neuroidss/FreeEEG32-alpha1.5/OpenVIBE/gdf/Screenshot from 2019-09-13 23-40-55.png

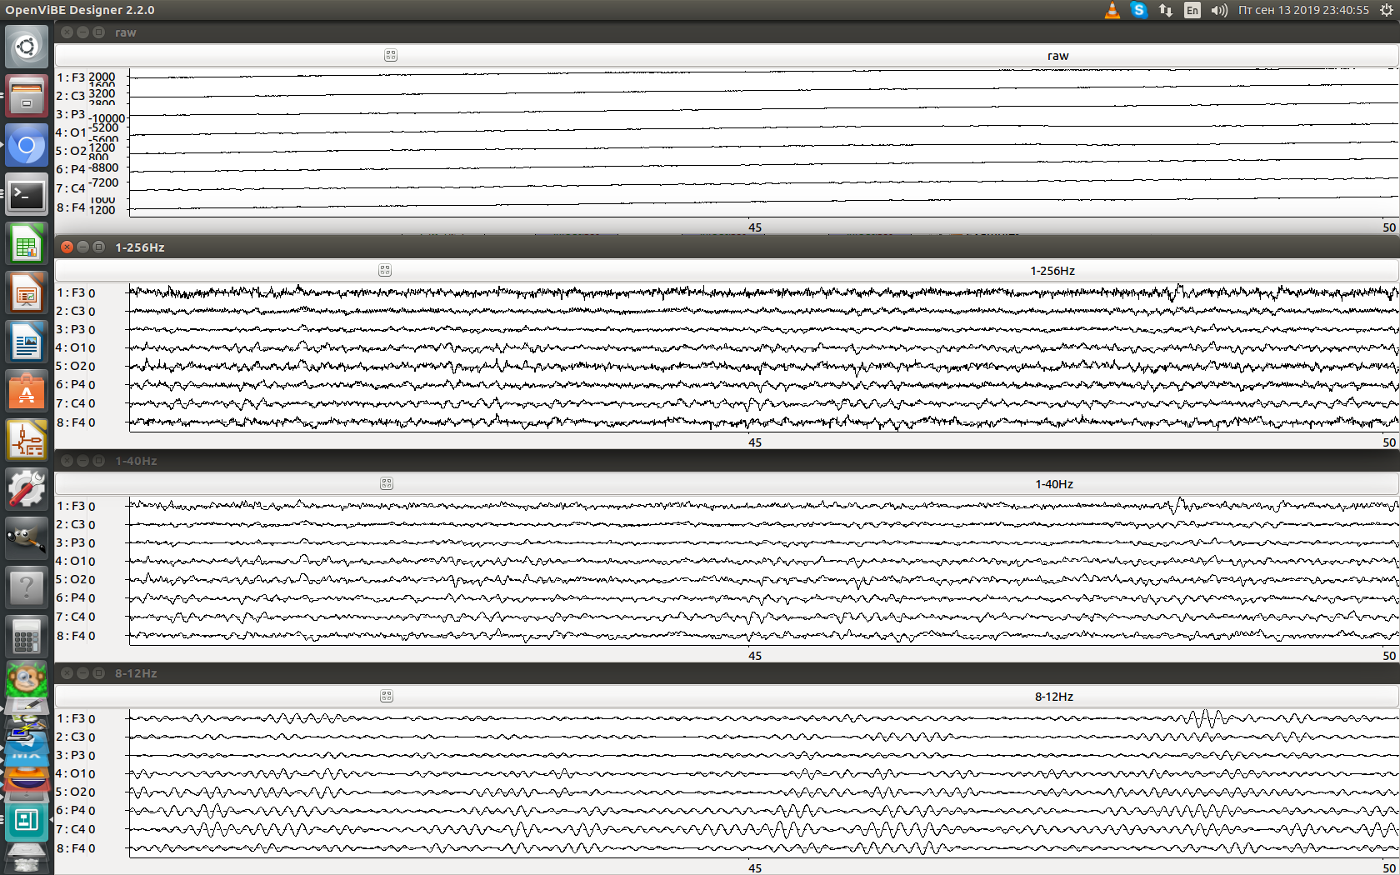
OpenVIBE/gdf/Screenshot from 2019-09-13 23-40-55.png
