neuroidss/FreeEEG32-alpha1.5/OpenVIBE/photo_2019-10-30_23-13-45.jpg

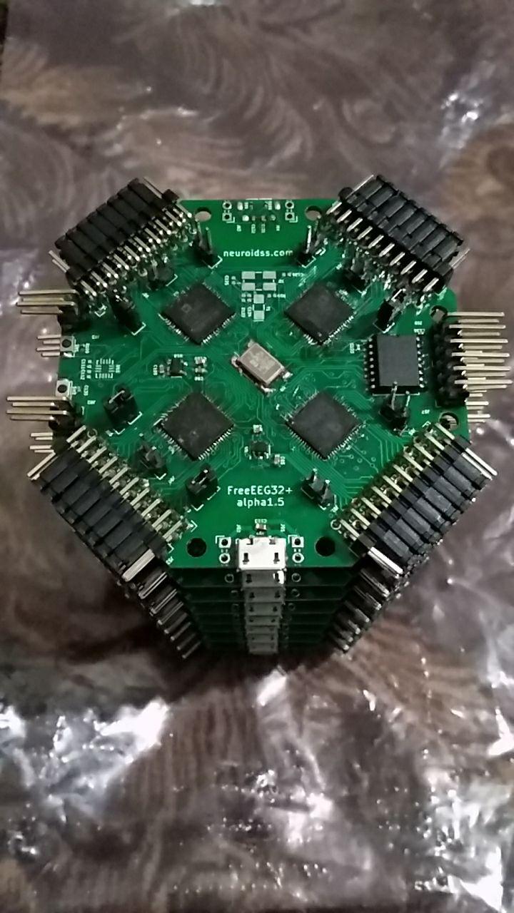
OpenVIBE/photo_2019-10-30_23-13-45.jpg
