neuroidss/FreeEEG32-alpha1.5/OpenVIBE/photo_2019-10-31_11-32-17.jpg

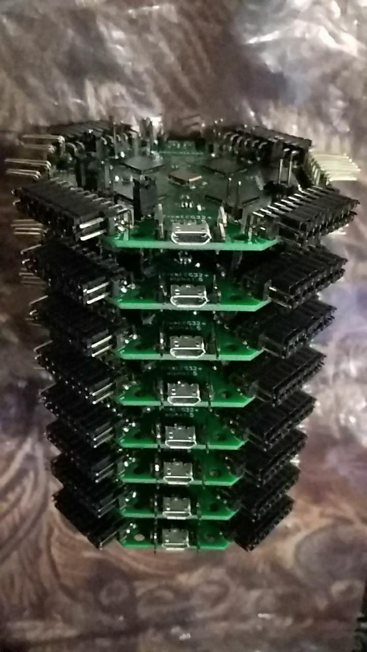
OpenVIBE/photo_2019-10-31_11-32-17.jpg
