neuroidss/FreeEEG32-alpha1.5/OpenVIBE/Screenshot from 2019-09-04 21-14-45.png

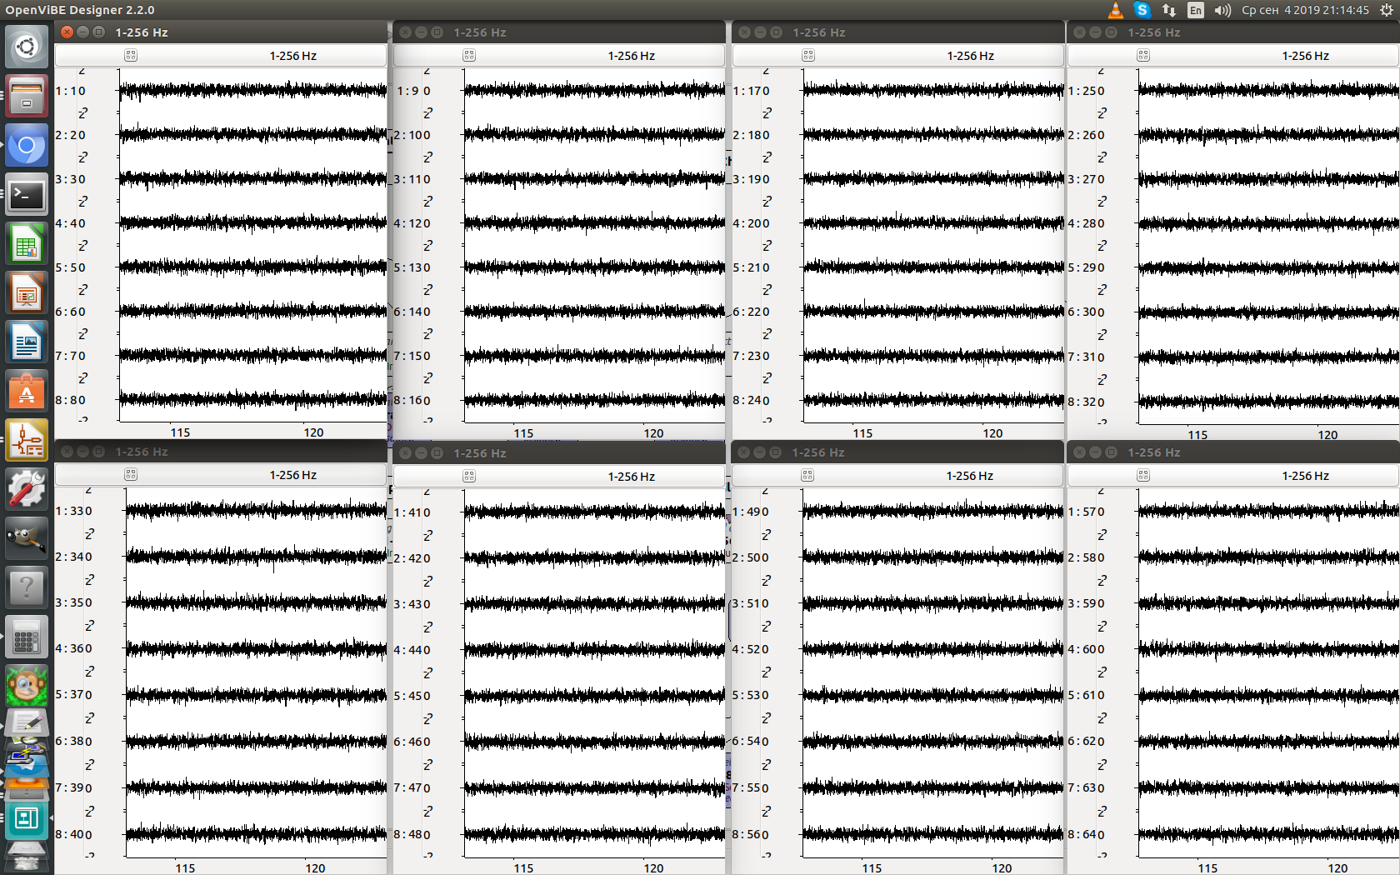
OpenVIBE/Screenshot from 2019-09-04 21-14-45.png
