neuroidss/FreeEEG32-alpha1.5/theta&gamma2octave/Screenshot from 2020-05-12 00-38-37.png

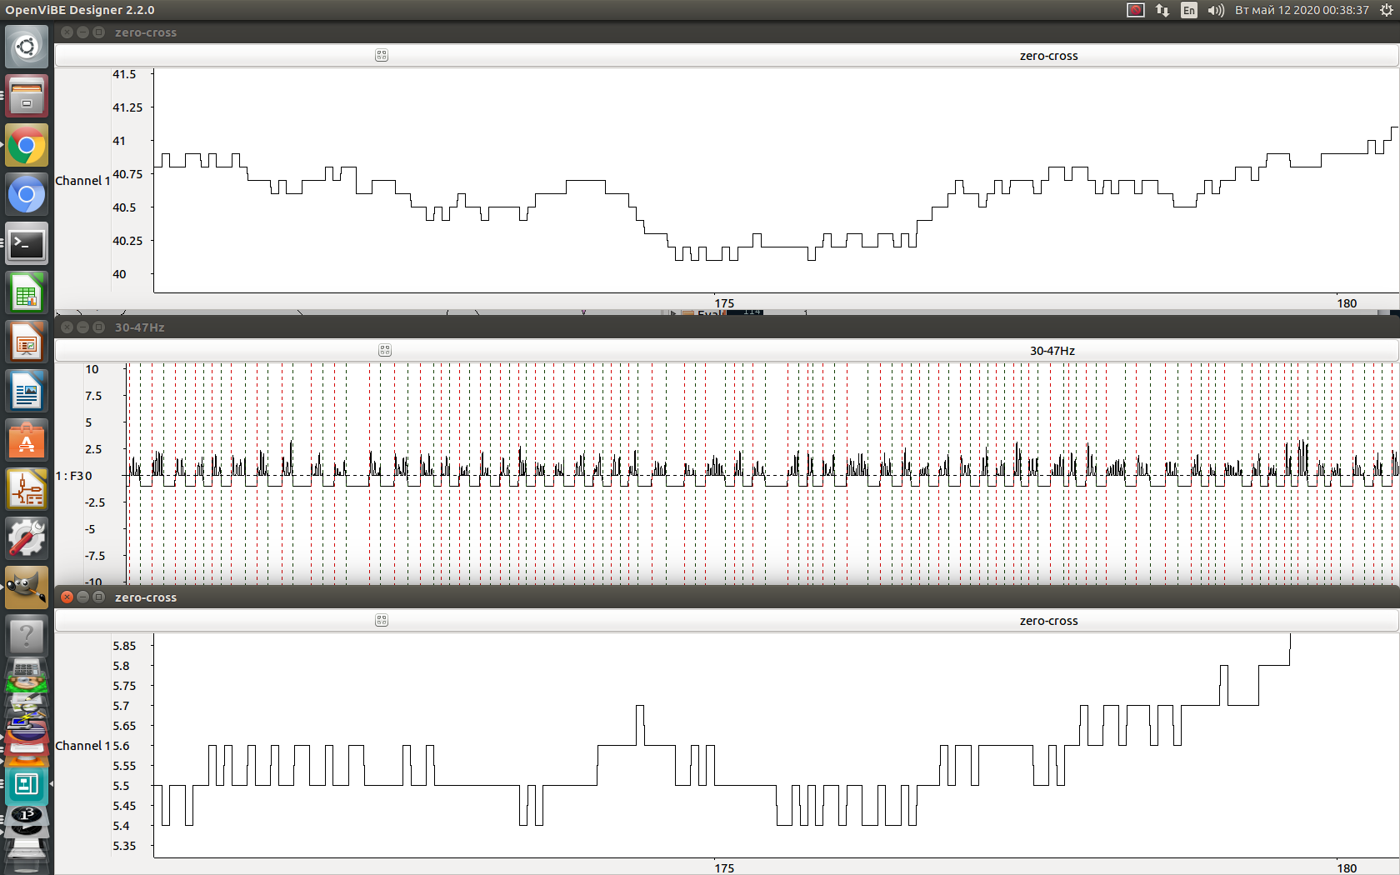
theta&gamma2octave/Screenshot from 2020-05-12 00-38-37.png
