neuroidss/FreeEEG32-alpha1.5/theta&gamma2octave/Screenshot_20200625-190515.png

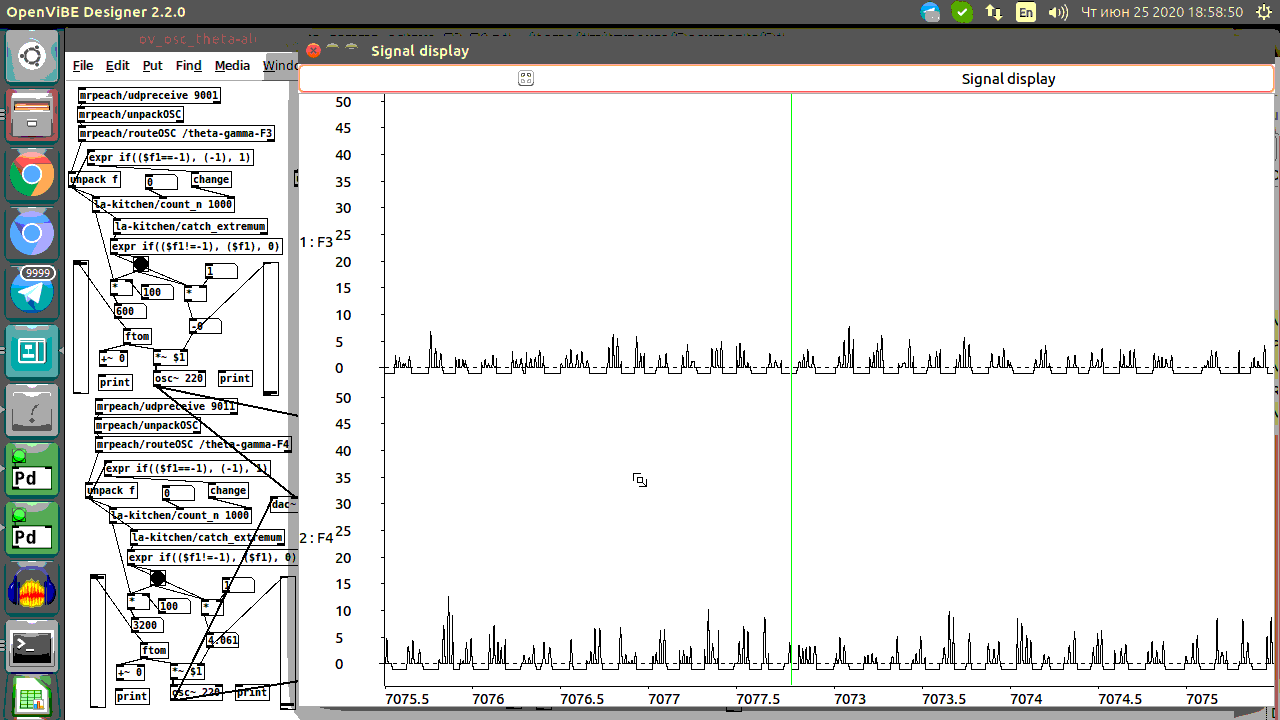
theta&gamma2octave/Screenshot_20200625-190515.png
