neuroidss/FreeEEG32-alpha1.5/theta&gamma2octave/Screenshot_20200629-193854.png

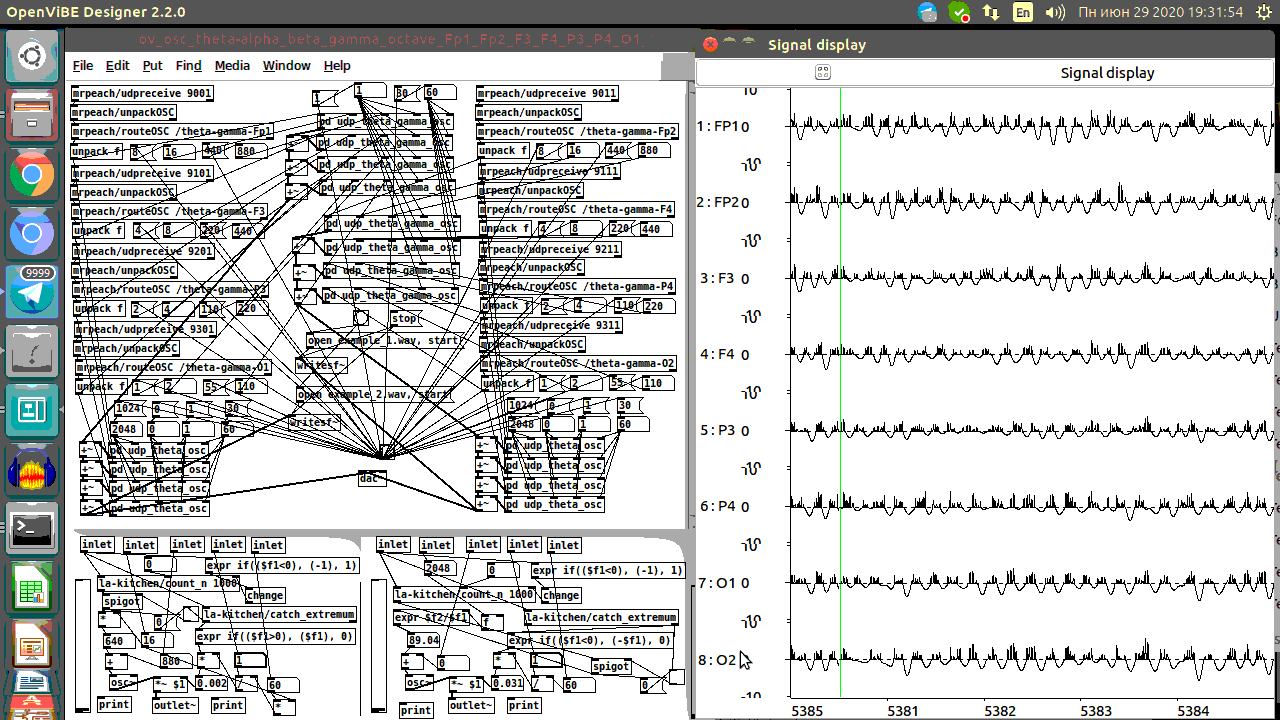
theta&gamma2octave/Screenshot_20200629-193854.png
